tadakado/mucon/images/picture10.jpeg

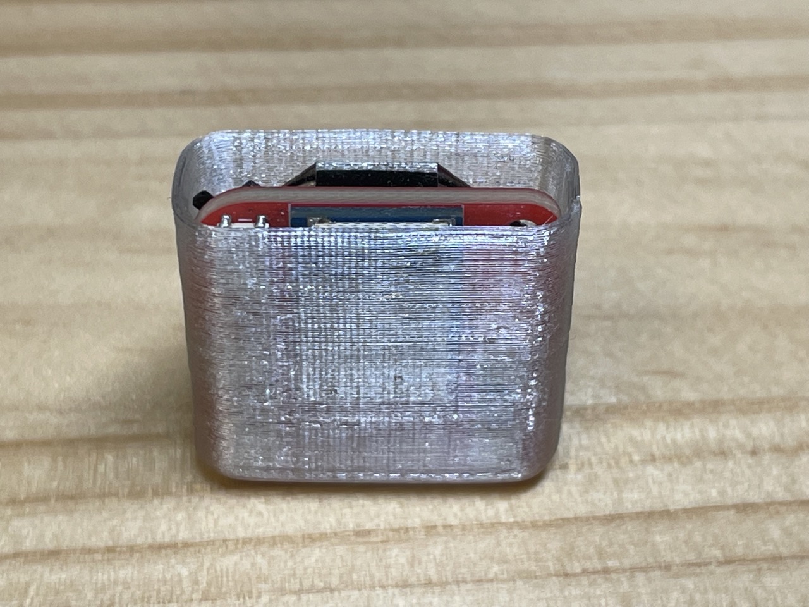
images/picture10.jpeg
