tadakado/mucon/images/picture11.jpeg

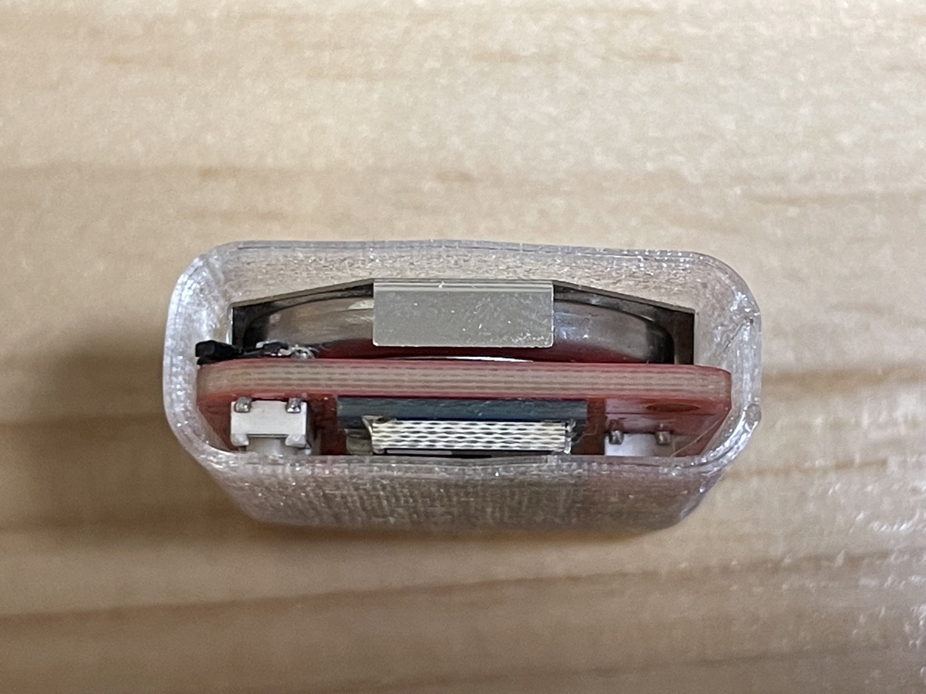
images/picture11.jpeg
